CCHS-Melbourne/Spectrogram/software/micropython/leds.py

import asyncio
from random import randint
from neopixel import NeoPixel
from machine import Pin
from time import ticks_us, ticks_diff

NUM_LEDS = 13 #50 #ugly work around for array out of bound error caused by ring buffer in mic.py
DEV_STATUS_LED_PIN=21
LEDS_PIN0 = 6
LEDS_PIN1 = 8
LEDS_PIN2 = 7

class Leds():
    def __init__(self):
        gpioS = Pin(DEV_STATUS_LED_PIN, Pin.OUT)
        gpio0 = Pin(LEDS_PIN0, Pin.OUT)
        gpio1 = Pin(LEDS_PIN1, Pin.OUT)
        gpio2 = Pin(LEDS_PIN2, Pin.OUT)
        self.status_pix = NeoPixel(gpioS, 1, )
        self.neopix0 = NeoPixel(gpio0, NUM_LEDS)
        self.neopix1 = NeoPixel(gpio1, NUM_LEDS)
        self.neopix2 = NeoPixel(gpio2, NUM_LEDS)
        self.led_list=[self.neopix0,self.neopix1,self.neopix2,self.status_pix]

    def __iter__(self):
        pass

    async def blink(self):
        for round in range(1000):
            self.neopix[0] = (randint(1,255), randint(1,255), randint(1,255))
            await asyncio.sleep_ms(50)
            self.neopix[0] = (randint(1,255), randint(1,255), randint(1,255))
            await asyncio.sleep_ms(50)
            self.neopix.write()

    async def light(self, led_nr, values):
        self.neopix[led_nr] = values
        await asyncio.sleep_ms(50)
        self.neopix.write()

    async def dance(self):
        await self.blink()

    async def show_hsv(self, led_arr_num, led_nr, hue, sat, val):
        #show_hsv time to pixel:  3068 µs
        t0 = ticks_us()
        rgb = await self.colorHSV(hue, sat, val)
        self.led_list[led_arr_num][led_nr] = rgb
#         self.neopix.write()
        t1 = ticks_us()
        #print(f'show_hsv time to pixel:{ticks_diff(t1, t0):6d} µs')
    
    async def write(self, led_arr_num):
        self.led_list[led_arr_num].write()
    
    #apparently not smooth
    async def fade_rgb(self, led_arr_num, led_nr, target_hue, steps=30):
        current_rgb = self.led_list[led_arr_num][led_nr]
        target_rgb = self.colorHSV(target_hue)
        for step in range(steps):
            # Linear interpolation
            blended = [
                current_rgb[i] + (target_rgb[i] - current_rgb[i]) * step // steps
                for i in range(3)
            ]
            np[pixel_index] = blended
            np.write()  # Blocking, but short
            await asyncio.sleep_ms(0)
     
#     async def fade_to_hsv(j,i, target_hue, sat, val, steps=30, delay_ms=10):
#         current_hue=rgb2hsv(self.led_list[led_arr_num][led_nr])
#         for step in range(steps):
#             # Interpolate HSV
#             blended_hue=blended_hue = current_hue + (target_hue - current_hue) * step // steps
#             self.led_list[led_arr_num][led_nr] = colourHSV(blended_hue,sat,val)  # Implement this too
#             np.write()
#             await asyncio.sleep_ms(0)
            
    async def colorHSV(self, hue, sat, val):
        # colorHSV time:    64 µs
        """
        Converts HSV color to rgb tuple and returns it.
        The logic is almost the same as in Adafruit NeoPixel library:
        https://github.com/adafruit/Adafruit_NeoPixel so all the credits for that
        go directly to them (license: https://github.com/adafruit/Adafruit_NeoPixel/blob/master/COPYING)

        :param hue: Hue component. Should be on interval 0..65535
        :param sat: Saturation component. Should be on interval 0..255
        :param val: Value component. Should be on interval 0..255
        :return: (r, g, b) tuple
        """

        t0 = ticks_us()
        #print("HSV value: ", hue, sat, val)

        if hue >= 65536:
            hue %= 65536

        hue = (hue * 1530 + 32768) // 65536
        if hue < 510:
            b = 0
            if hue < 255:
                r = 255
                g = hue
            else:
                r = 510 - hue
                g = 255
        elif hue < 1020:
            r = 0
            if hue < 765:
                g = 255
                b = hue - 510
            else:
                g = 1020 - hue
                b = 255
        elif hue < 1530:
            g = 0
            if hue < 1275:
                r = hue - 1020
                b = 255
            else:
                r = 255
                b = 1530 - hue
        else:
            r = 255
            g = 0
            b = 0

        v1 = 1 + val
        s1 = 1 + sat
        s2 = 255 - sat

        r = ((((r * s1) >> 8) + s2) * v1) >> 8
        g = ((((g * s1) >> 8) + s2) * v1) >> 8
        b = ((((b * s1) >> 8) + s2) * v1) >> 8

        #print("RGB value: ", r, g, b)

        t1 = ticks_us()
        #print(f'colorHSV time:{ticks_diff(t1, t0):6d} µs')

        return (r, g, b)
